tkleisas/groovebox/docs/themes.png

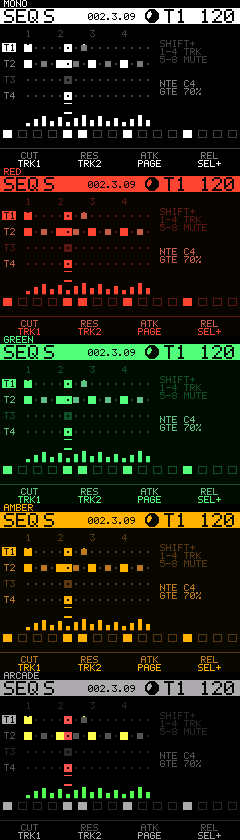
docs/themes.png
