tkleisas/groovebox/docs/widgets.png

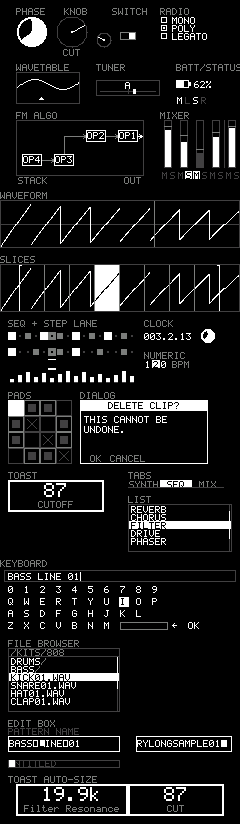
docs/widgets.png
