tkleisas/groovebox/nsr2/panel_mockup_nsr2.png

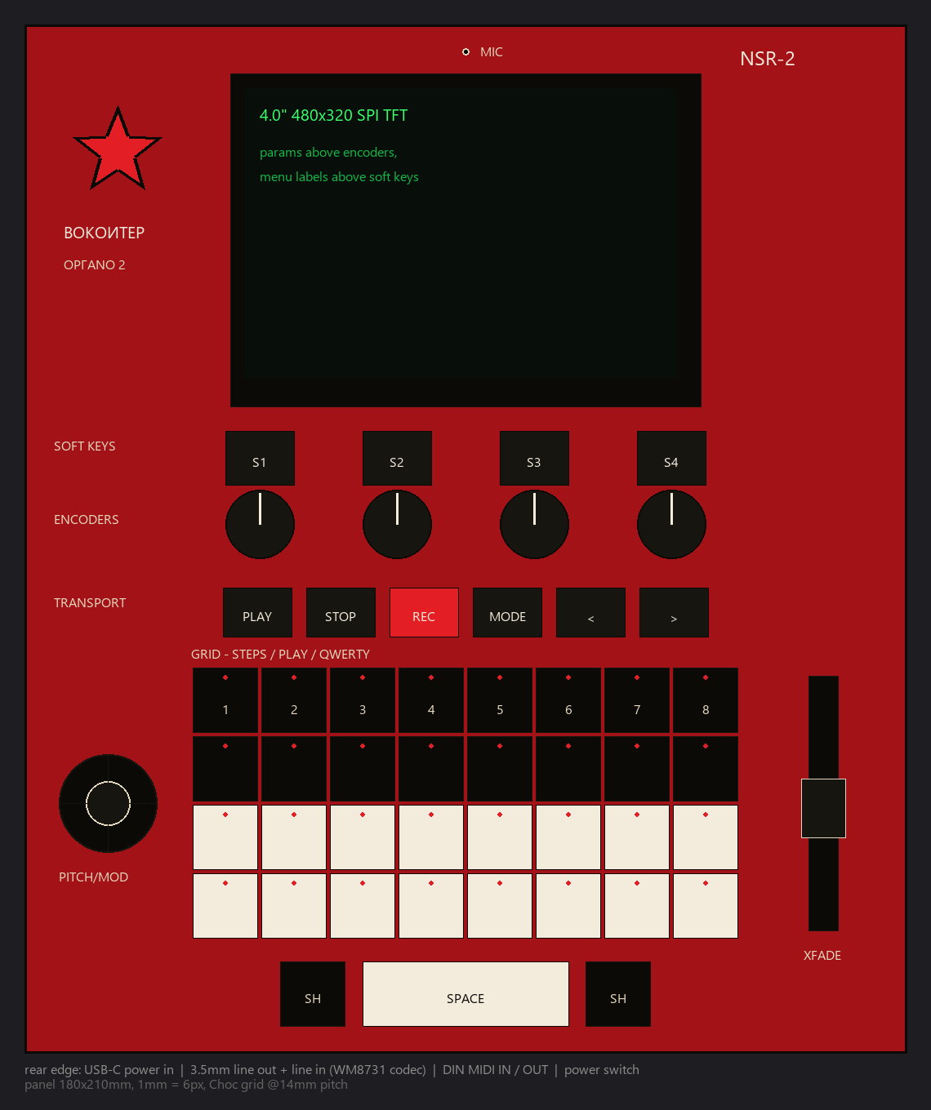
nsr2/panel_mockup_nsr2.png
