tkleisas/groovebox/nsr2/hardware/brain/brain.kicad_sch

## KiCad design nsr2/hardware/brain/brain.kicad_sch (2026-09-04)

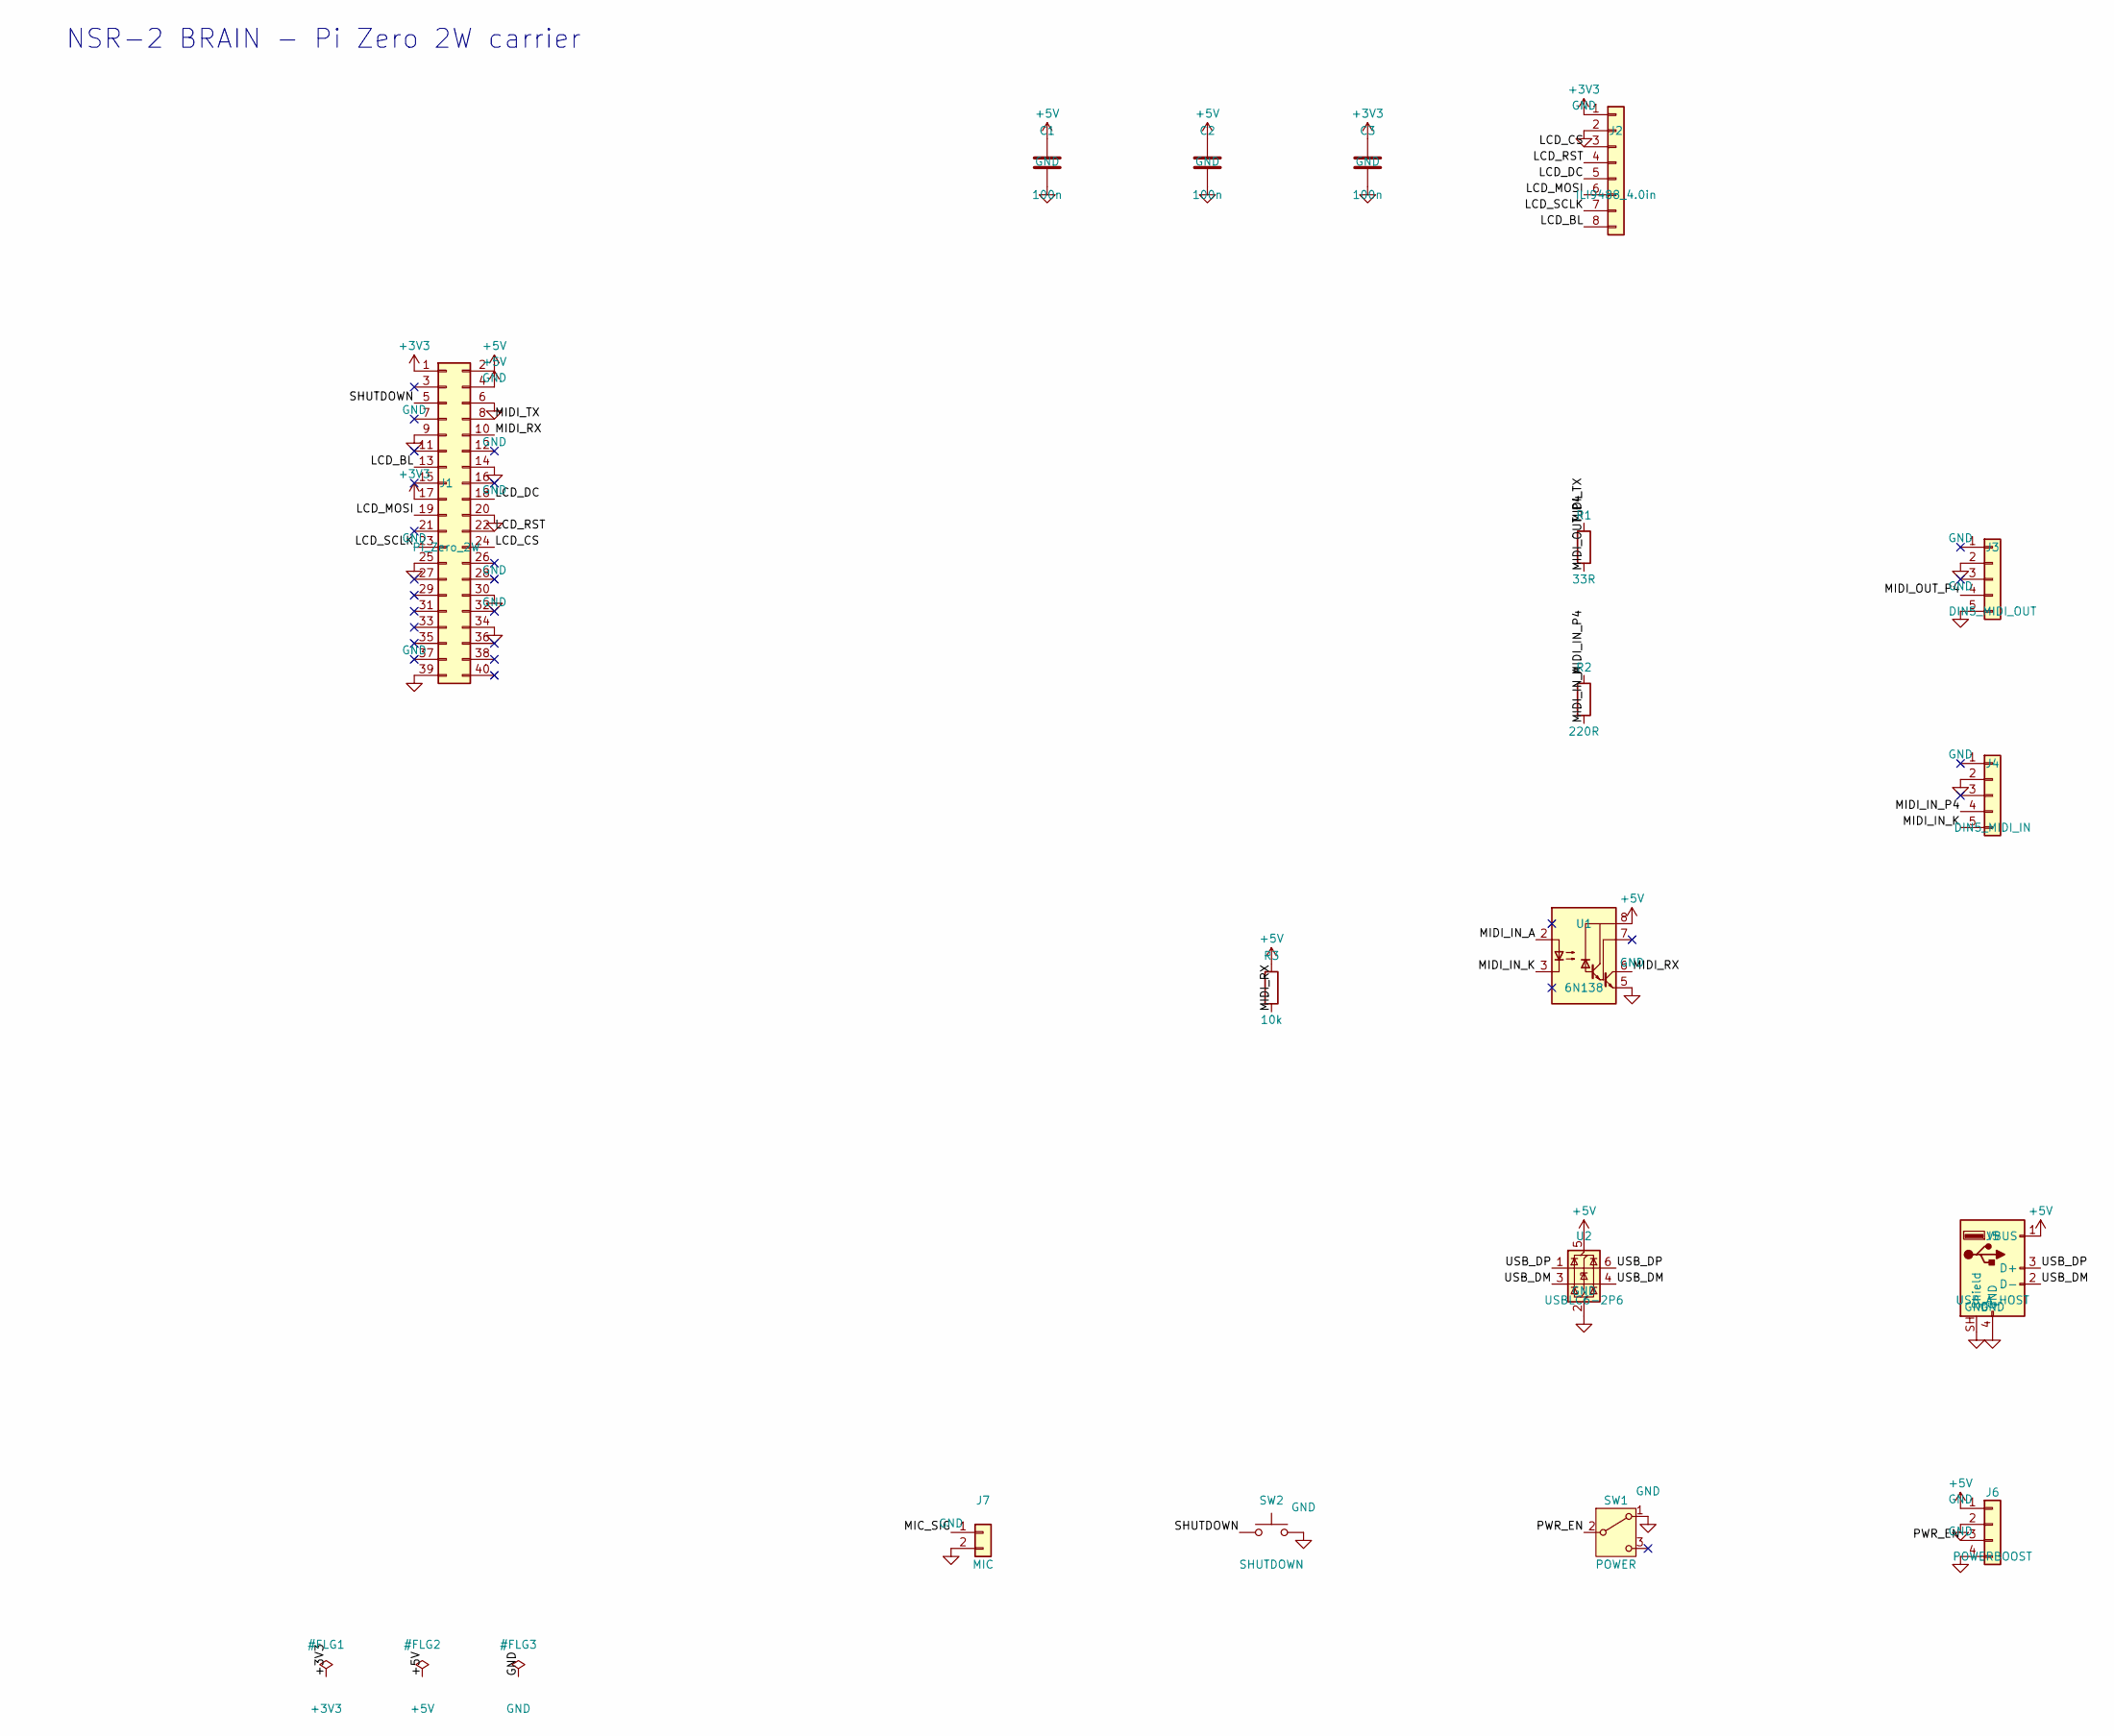
[picture p11: schematic brain.kicad_sch]

Parts:
C1, C2, C3: 100n; C_0805_2012Metric
J1: Pi_Zero_2W; PinSocket_2x20_P2.54mm_Vertical
J2: ILI9488_4.0in; PinHeader_1x08_P2.54mm_Horizontal
J3: DIN5_MIDI_OUT; DIN5-RA-PTH
J4: DIN5_MIDI_IN; DIN5-RA-PTH
J5: USB_A_HOST; USB_A_Connfly_DS1098_Horizontal
J6: POWERBOOST; JST_XH_B4B-XH-A_1x04_P2.50mm_Vertical
J7: MIC; JST_XH_B2B-XH-A_1x02_P2.50mm_Vertical
R1: 33R; R_0805_2012Metric
R2: 220R; R_0805_2012Metric
R3: 10k; R_0805_2012Metric
SW1: POWER; SW_SPDT_SLIDE_THT
SW2: SHUTDOWN; SW_PUSH_6mm
U1: 6N138; DIP-8_W7.62mm
U2: USBLC6-2P6; SOT-23-6

Connections:
+3V3: C3.1, J1.1, J1.17, J2.1
+5V: C1.1, C2.1, J1.2, J1.4, J5.1 (VBUS), J6.1, R3.1, U1.8 (VCC), U2.5 (VBUS)
GND: C1.2, C2.2, C3.2, J1.6, J1.9, J1.14, J1.20, J1.25, J1.30, J1.34, J1.39, J2.2, J3.2, J3.5, J4.2, J5.4 (GND), J5.SH (Shield), J6.2, J6.4, J7.2, SW1.1 (A), SW2.2, U1.5 (GND), U2.2 (GND)
LCD_BL: J1.13, J2.8
LCD_CS: J1.24, J2.3
LCD_DC: J1.18, J2.5
LCD_MOSI: J1.19, J2.6
LCD_RST: J1.22, J2.4
LCD_SCLK: J1.23, J2.7
MIC_SIG: J7.1
MIDI_IN_A: R2.2, U1.2 (C1)
MIDI_IN_K: J4.5, U1.3 (C2)
MIDI_IN_P4: J4.4, R2.1
MIDI_OUT_P4: J3.4, R1.2
MIDI_RX: J1.10, R3.2, U1.6 (VO2)
MIDI_TX: J1.8, R1.1
PWR_EN: J6.3, SW1.2 (B)
SHUTDOWN: J1.5, SW2.1
USB_DM: J5.2 (D-), U2.3 (I/O2), U2.4 (I/O2)
USB_DP: J5.3 (D+), U2.1 (I/O1), U2.6 (I/O1)

Notes on the sheet:
NSR-2 BRAIN - Pi Zero 2W carrier
