tkleisas/groovebox/nsr2/hardware/io/io.kicad_sch

## KiCad design nsr2/hardware/io/io.kicad_sch (2026-09-04)

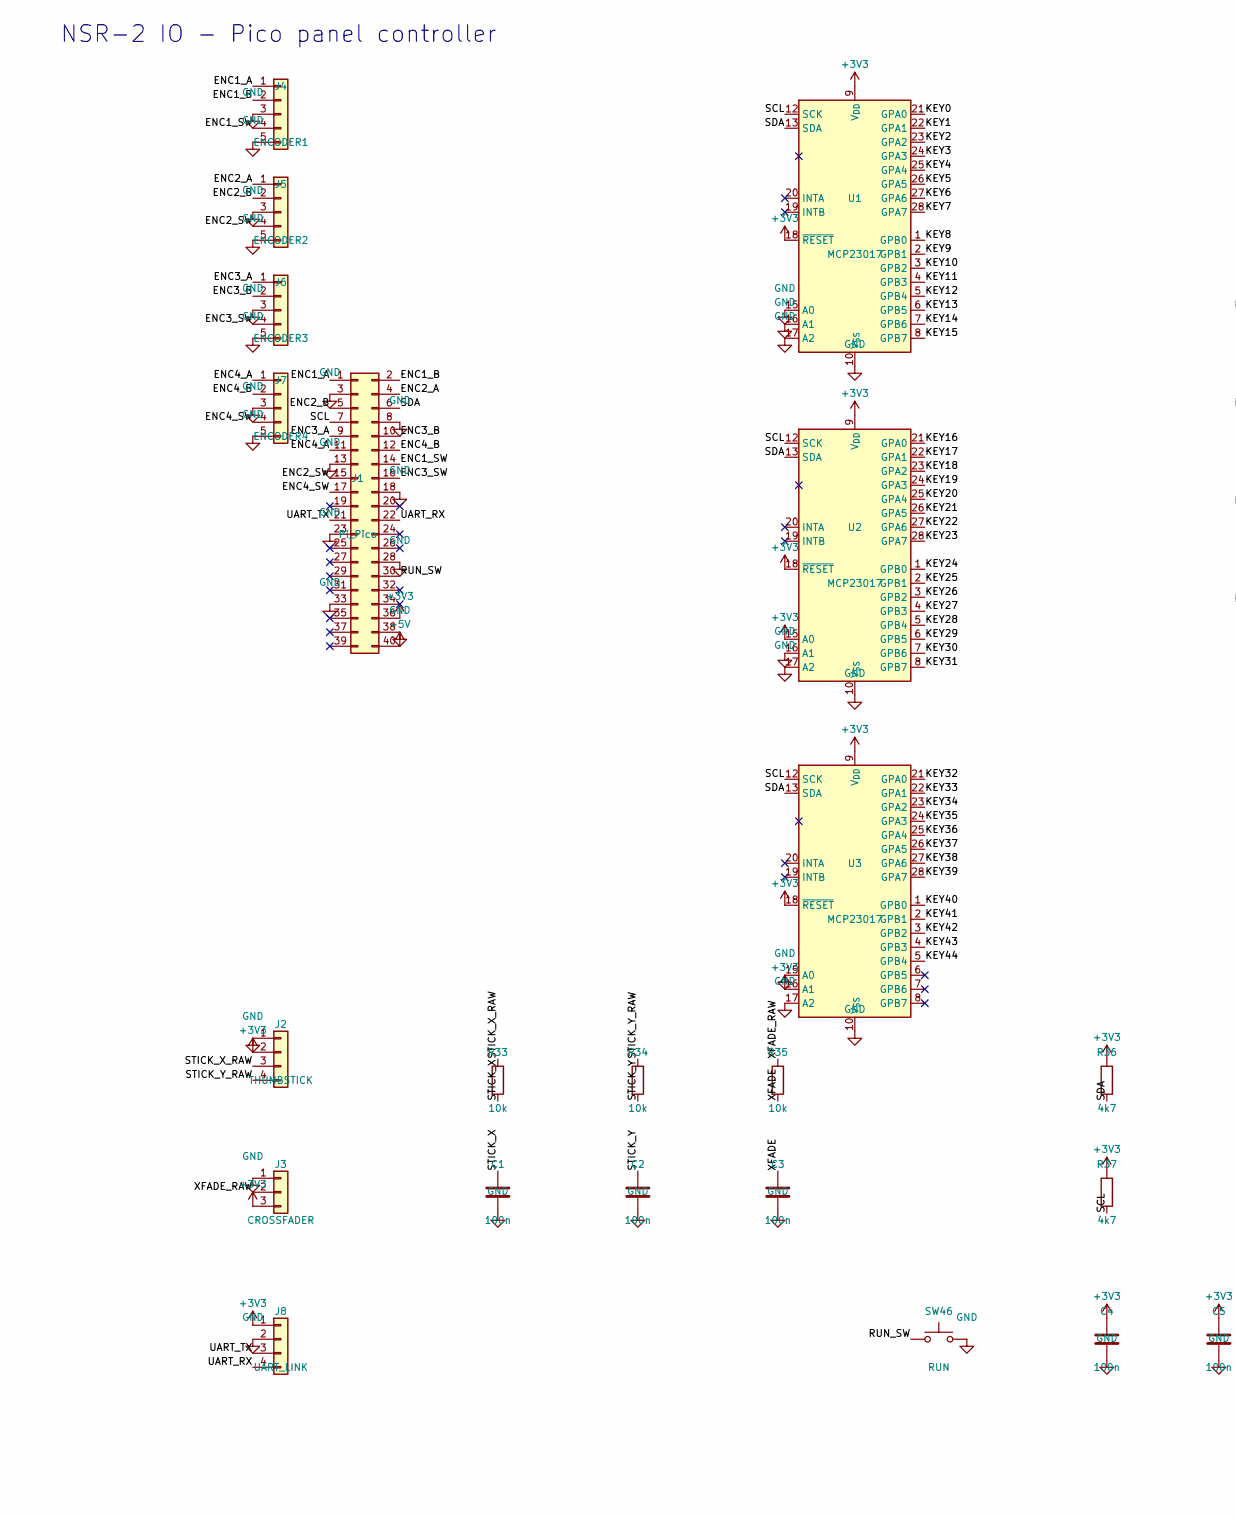
[picture p12: schematic io.kicad_sch, part in row 1, column 1]

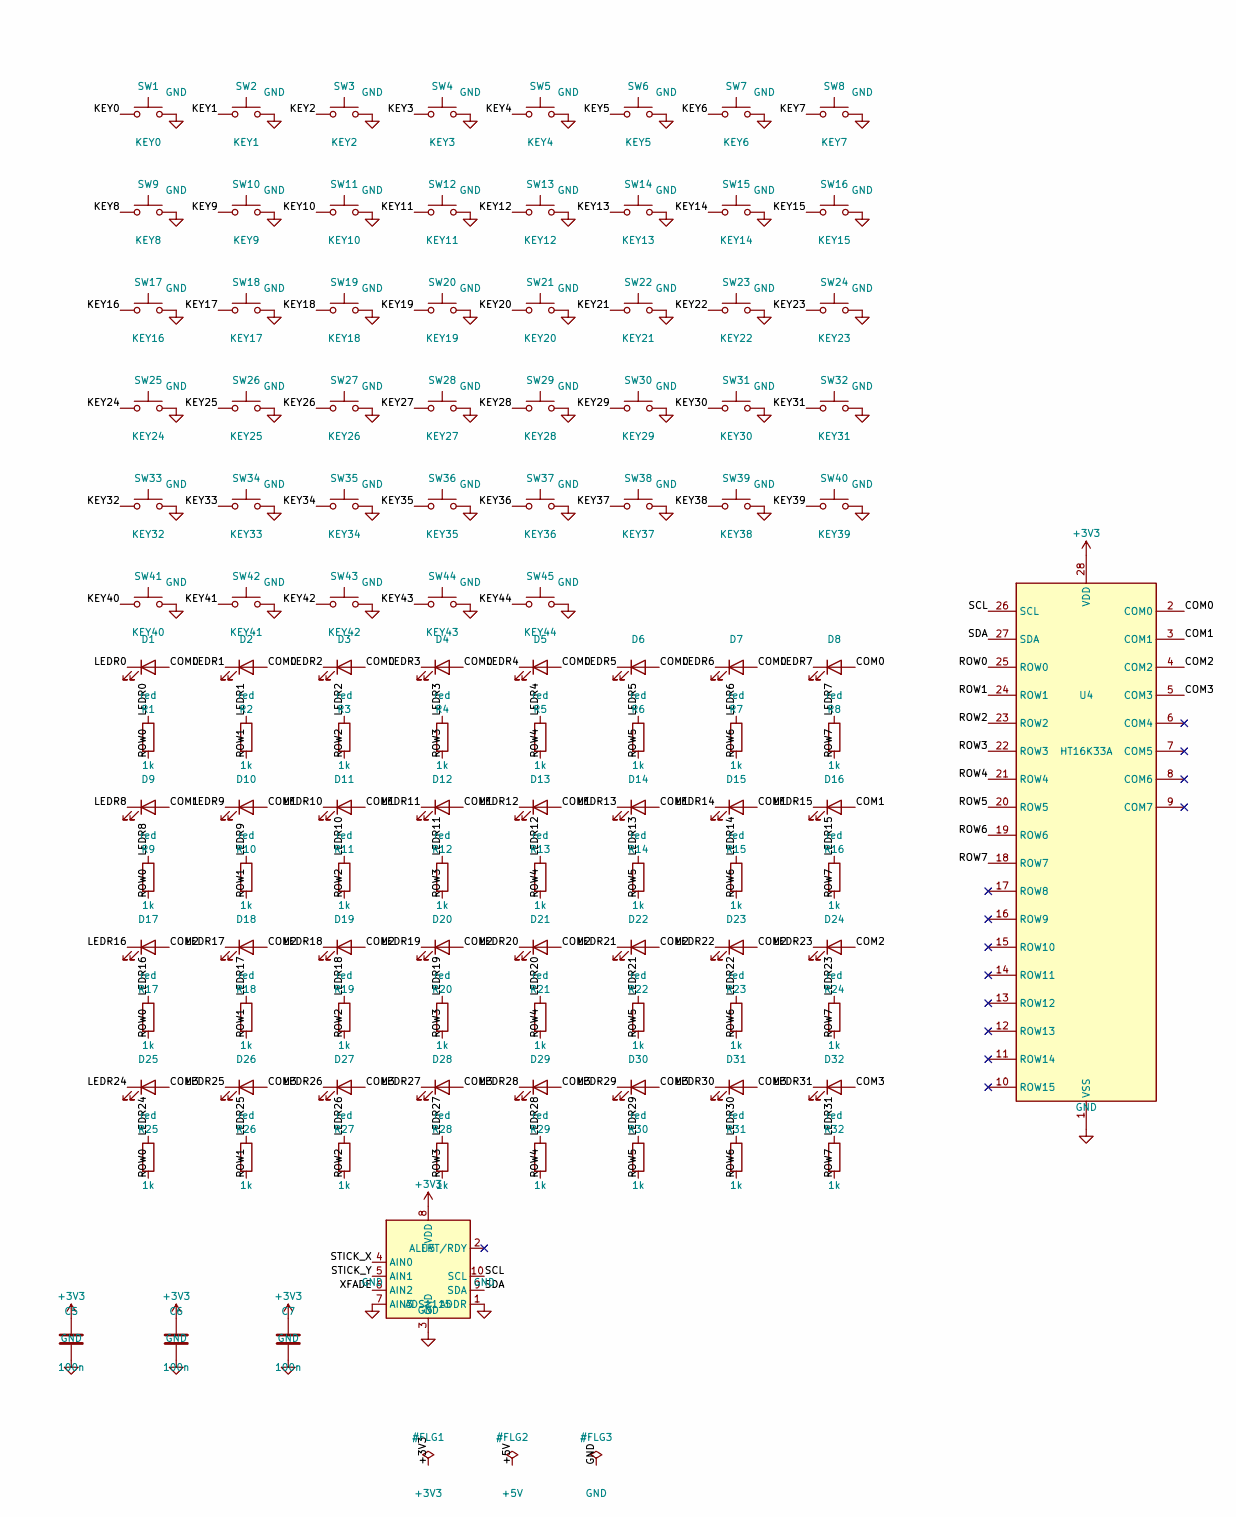
[picture p13: schematic io.kicad_sch, part in row 1, column 2]

Parts:
C1, C2, C3, C4, C5, C6, C7: 100n; C_0805_2012Metric
D1, D2, D3, D4, D5, D6, D7, D8, D9, D10, D11, D12, D13, D14, D15, D16, D17, D18, D19, D20, D21, D22, D23, D24, D25, D26, D27, D28, D29, D30, D31, D32: red; LED_0603_1608Metric
J1: Pi_Pico; PinSocket_2x20_P2.54mm_Vertical
J2: THUMBSTICK; JST_XH_B4B-XH-A_1x04_P2.50mm_Vertical
J3: CROSSFADER; JST_XH_B3B-XH-A_1x03_P2.50mm_Vertical
J4: ENCODER1; JST_XH_B5B-XH-A_1x05_P2.50mm_Vertical
J5: ENCODER2; JST_XH_B5B-XH-A_1x05_P2.50mm_Vertical
J6: ENCODER3; JST_XH_B5B-XH-A_1x05_P2.50mm_Vertical
J7: ENCODER4; JST_XH_B5B-XH-A_1x05_P2.50mm_Vertical
J8: UART_LINK; JST_XH_B4B-XH-A_1x04_P2.50mm_Vertical
R1, R2, R3, R4, R5, R6, R7, R8, R9, R10, R11, R12, R13, R14, R15, R16, R17, R18, R19, R20, R21, R22, R23, R24, R25, R26, R27, R28, R29, R30, R31, R32: 1k; R_0805_2012Metric
R33, R34, R35: 10k; R_0805_2012Metric
R36, R37: 4k7; R_0805_2012Metric
SW1: KEY0; SW_Hotswap_Kailh_Choc_V1
SW2: KEY1; SW_Hotswap_Kailh_Choc_V1
SW3: KEY2; SW_Hotswap_Kailh_Choc_V1
SW4: KEY3; SW_Hotswap_Kailh_Choc_V1
SW5: KEY4; SW_Hotswap_Kailh_Choc_V1
SW6: KEY5; SW_Hotswap_Kailh_Choc_V1
SW7: KEY6; SW_Hotswap_Kailh_Choc_V1
SW8: KEY7; SW_Hotswap_Kailh_Choc_V1
SW9: KEY8; SW_Hotswap_Kailh_Choc_V1
SW10: KEY9; SW_Hotswap_Kailh_Choc_V1
SW11: KEY10; SW_Hotswap_Kailh_Choc_V1
SW12: KEY11; SW_Hotswap_Kailh_Choc_V1
SW13: KEY12; SW_Hotswap_Kailh_Choc_V1
SW14: KEY13; SW_Hotswap_Kailh_Choc_V1
SW15: KEY14; SW_Hotswap_Kailh_Choc_V1
SW16: KEY15; SW_Hotswap_Kailh_Choc_V1
SW17: KEY16; SW_Hotswap_Kailh_Choc_V1
SW18: KEY17; SW_Hotswap_Kailh_Choc_V1
SW19: KEY18; SW_Hotswap_Kailh_Choc_V1
SW20: KEY19; SW_Hotswap_Kailh_Choc_V1
SW21: KEY20; SW_Hotswap_Kailh_Choc_V1
SW22: KEY21; SW_Hotswap_Kailh_Choc_V1
SW23: KEY22; SW_Hotswap_Kailh_Choc_V1
SW24: KEY23; SW_Hotswap_Kailh_Choc_V1
SW25: KEY24; SW_Hotswap_Kailh_Choc_V1
SW26: KEY25; SW_Hotswap_Kailh_Choc_V1
SW27: KEY26; SW_Hotswap_Kailh_Choc_V1
SW28: KEY27; SW_Hotswap_Kailh_Choc_V1
SW29: KEY28; SW_Hotswap_Kailh_Choc_V1
SW30: KEY29; SW_Hotswap_Kailh_Choc_V1
SW31: KEY30; SW_Hotswap_Kailh_Choc_V1
SW32: KEY31; SW_Hotswap_Kailh_Choc_V1
SW33: KEY32; SW_Hotswap_Kailh_Choc_V1
SW34: KEY33; SW_Hotswap_Kailh_Choc_V1
SW35: KEY34; SW_Hotswap_Kailh_Choc_V1
SW36: KEY35; SW_Hotswap_Kailh_Choc_V1
SW37: KEY36; SW_Hotswap_Kailh_Choc_V1
SW38: KEY37; SW_Hotswap_Kailh_Choc_V1
SW39: KEY38; SW_Hotswap_Kailh_Choc_V1
SW40: KEY39; SW_Hotswap_Kailh_Choc_V1
SW41: KEY40; SW_Hotswap_Kailh_Choc_V1
SW42: KEY41; SW_Hotswap_Kailh_Choc_V1
SW43: KEY42; SW_Hotswap_Kailh_Choc_V1
SW44: KEY43; SW_Hotswap_Kailh_Choc_V1
SW45: KEY44; SW_Hotswap_Kailh_Choc_V1
SW46: RUN; SW_PUSH_6mm
U1, U2, U3: MCP23017; SSOP-28_5.3x10.2mm_P0.65mm
U4: HT16K33A; SSOP-28_5.3x10.2mm_P0.65mm
U5: ADS1115; MSOP-10_3x3mm_P0.5mm

Connections:
+3V3: C4.1, C5.1, C6.1, C7.1, J1.36, J2.2, J3.3, J8.1, R36.1, R37.1, U1.9 (V_{DD}), U1.18 (~RESET), U2.9 (V_{DD}), U2.15 (A0), U2.18 (~RESET), U3.9 (V_{DD}), U3.16 (A1), U3.18 (~RESET), U4.28 (VDD), U5.8 (VDD)
+5V: J1.40
COM0: D1.2 (A), D2.2 (A), D3.2 (A), D4.2 (A), D5.2 (A), D6.2 (A), D7.2 (A), D8.2 (A), U4.2 (COM0)
COM1: D9.2 (A), D10.2 (A), D11.2 (A), D12.2 (A), D13.2 (A), D14.2 (A), D15.2 (A), D16.2 (A), U4.3 (COM1)
COM2: D17.2 (A), D18.2 (A), D19.2 (A), D20.2 (A), D21.2 (A), D22.2 (A), D23.2 (A), D24.2 (A), U4.4 (COM2)
COM3: D25.2 (A), D26.2 (A), D27.2 (A), D28.2 (A), D29.2 (A), D30.2 (A), D31.2 (A), D32.2 (A), U4.5 (COM3)
ENC1_A: J1.1, J4.1
ENC1_B: J1.2, J4.2
ENC1_SW: J1.14, J4.4
ENC2_A: J1.4, J5.1
ENC2_B: J1.5, J5.2
ENC2_SW: J1.15, J5.4
ENC3_A: J1.9, J6.1
ENC3_B: J1.10, J6.2
ENC3_SW: J1.16, J6.4
ENC4_A: J1.11, J7.1
ENC4_B: J1.12, J7.2
ENC4_SW: J1.17, J7.4
GND: C1.2, C2.2, C3.2, C4.2, C5.2, C6.2, C7.2, J1.3, J1.8, J1.13, J1.18, J1.23, J1.28, J1.33, J1.38, J2.1, J3.1, J4.3, J4.5, J5.3, J5.5, J6.3, J6.5, J7.3, J7.5, J8.2, SW1.2, SW2.2, SW3.2, SW4.2, SW5.2, SW6.2, SW7.2, SW8.2, SW9.2, SW10.2, SW11.2, SW12.2, SW13.2, SW14.2, SW15.2, SW16.2, SW17.2, SW18.2, SW19.2, SW20.2, SW21.2, SW22.2, SW23.2, SW24.2, SW25.2, SW26.2, SW27.2, SW28.2, SW29.2, SW30.2, SW31.2, SW32.2, SW33.2, SW34.2, SW35.2, SW36.2, SW37.2, SW38.2, SW39.2, SW40.2, SW41.2, SW42.2, SW43.2, SW44.2, SW45.2, SW46.2, U1.10 (V_{SS}), U1.15 (A0), U1.16 (A1), U1.17 (A2), U2.10 (V_{SS}), U2.16 (A1), U2.17 (A2), U3.10 (V_{SS}), U3.15 (A0), U3.17 (A2), U4.1 (VSS), U5.1 (ADDR), U5.3 (GND), U5.7 (AIN3)
KEY0: SW1.1, U1.21 (GPA0)
KEY1: SW2.1, U1.22 (GPA1)
KEY2: SW3.1, U1.23 (GPA2)
KEY3: SW4.1, U1.24 (GPA3)
KEY4: SW5.1, U1.25 (GPA4)
KEY5: SW6.1, U1.26 (GPA5)
KEY6: SW7.1, U1.27 (GPA6)
KEY7: SW8.1, U1.28 (GPA7)
KEY8: SW9.1, U1.1 (GPB0)
KEY9: SW10.1, U1.2 (GPB1)
KEY10: SW11.1, U1.3 (GPB2)
KEY11: SW12.1, U1.4 (GPB3)
KEY12: SW13.1, U1.5 (GPB4)
KEY13: SW14.1, U1.6 (GPB5)
KEY14: SW15.1, U1.7 (GPB6)
KEY15: SW16.1, U1.8 (GPB7)
KEY16: SW17.1, U2.21 (GPA0)
KEY17: SW18.1, U2.22 (GPA1)
KEY18: SW19.1, U2.23 (GPA2)
KEY19: SW20.1, U2.24 (GPA3)
KEY20: SW21.1, U2.25 (GPA4)
KEY21: SW22.1, U2.26 (GPA5)
KEY22: SW23.1, U2.27 (GPA6)
KEY23: SW24.1, U2.28 (GPA7)
KEY24: SW25.1, U2.1 (GPB0)
KEY25: SW26.1, U2.2 (GPB1)
KEY26: SW27.1, U2.3 (GPB2)
KEY27: SW28.1, U2.4 (GPB3)
KEY28: SW29.1, U2.5 (GPB4)
KEY29: SW30.1, U2.6 (GPB5)
KEY30: SW31.1, U2.7 (GPB6)
KEY31: SW32.1, U2.8 (GPB7)
KEY32: SW33.1, U3.21 (GPA0)
KEY33: SW34.1, U3.22 (GPA1)
KEY34: SW35.1, U3.23 (GPA2)
KEY35: SW36.1, U3.24 (GPA3)
KEY36: SW37.1, U3.25 (GPA4)
KEY37: SW38.1, U3.26 (GPA5)
KEY38: SW39.1, U3.27 (GPA6)
KEY39: SW40.1, U3.28 (GPA7)
KEY40: SW41.1, U3.1 (GPB0)
KEY41: SW42.1, U3.2 (GPB1)
KEY42: SW43.1, U3.3 (GPB2)
KEY43: SW44.1, U3.4 (GPB3)
KEY44: SW45.1, U3.5 (GPB4)
LEDR0: D1.1 (K), R1.1
LEDR1: D2.1 (K), R2.1
LEDR2: D3.1 (K), R3.1
LEDR3: D4.1 (K), R4.1
LEDR4: D5.1 (K), R5.1
LEDR5: D6.1 (K), R6.1
LEDR6: D7.1 (K), R7.1
LEDR7: D8.1 (K), R8.1
LEDR8: D9.1 (K), R9.1
LEDR9: D10.1 (K), R10.1
LEDR10: D11.1 (K), R11.1
LEDR11: D12.1 (K), R12.1
LEDR12: D13.1 (K), R13.1
LEDR13: D14.1 (K), R14.1
LEDR14: D15.1 (K), R15.1
LEDR15: D16.1 (K), R16.1
LEDR16: D17.1 (K), R17.1
LEDR17: D18.1 (K), R18.1
LEDR18: D19.1 (K), R19.1
LEDR19: D20.1 (K), R20.1
LEDR20: D21.1 (K), R21.1
LEDR21: D22.1 (K), R22.1
LEDR22: D23.1 (K), R23.1
LEDR23: D24.1 (K), R24.1
LEDR24: D25.1 (K), R25.1
LEDR25: D26.1 (K), R26.1
LEDR26: D27.1 (K), R27.1
LEDR27: D28.1 (K), R28.1
LEDR28: D29.1 (K), R29.1
LEDR29: D30.1 (K), R30.1
LEDR30: D31.1 (K), R31.1
LEDR31: D32.1 (K), R32.1
ROW0: R1.2, R9.2, R17.2, R25.2, U4.25 (ROW0)
ROW1: R2.2, R10.2, R18.2, R26.2, U4.24 (ROW1)
ROW2: R3.2, R11.2, R19.2, R27.2, U4.23 (ROW2)
ROW3: R4.2, R12.2, R20.2, R28.2, U4.22 (ROW3)
ROW4: R5.2, R13.2, R21.2, R29.2, U4.21 (ROW4)
ROW5: R6.2, R14.2, R22.2, R30.2, U4.20 (ROW5)
ROW6: R7.2, R15.2, R23.2, R31.2, U4.19 (ROW6)
ROW7: R8.2, R16.2, R24.2, R32.2, U4.18 (ROW7)
RUN_SW: J1.30, SW46.1
SCL: J1.7, R37.2, U1.12 (SCK), U2.12 (SCK), U3.12 (SCK), U4.26 (SCL), U5.10 (SCL)
SDA: J1.6, R36.2, U1.13 (SDA), U2.13 (SDA), U3.13 (SDA), U4.27 (SDA), U5.9 (SDA)
STICK_X: C1.1, R33.2, U5.4 (AIN0)
STICK_X_RAW: J2.3, R33.1
STICK_Y: C2.1, R34.2, U5.5 (AIN1)
STICK_Y_RAW: J2.4, R34.1
UART_RX: J1.22, J8.4
UART_TX: J1.21, J8.3
XFADE: C3.1, R35.2, U5.6 (AIN2)
XFADE_RAW: J3.2, R35.1

Notes on the sheet:
NSR-2 IO - Pico panel controller
