tkleisas/groovebox/emulator/src/ui.h

#pragma once

// Tiny software renderer for the 240x160 RGB565 display, in the style
// of docs/ui_mockup.png (Elektron-like, monochrome): inverted header
// bar (page name + BPM), parameter rows (dim name, bright value, bar),
// inverse-video selected row, LED row, footer with encoder / soft-key
// assignments.
//
// Pages (UiState::page): 0 = SYNTH (param rows), 1 = SEQ
// (SequencerWidget), 2 = MIXER (MixerWidget). Widget geometry lives in
// widgets.h; all widget bboxes follow the 8 px grid rule.

#include <cstdint>
#include "font5x7.h"
#include "hal.h" // kDisplayW / kDisplayH
#include "widgets.h"

namespace gb {

struct UiParam {
    const char* name;
    int value; // 0..127; -1 = unbound (renders dim "—")
};

struct UiState {
    const char* pageName = "SYNTH"; // page 0 title (SYNTH / DRUMS)
    // INST page on drum tracks: the edit pad (last-played voice), drawn
    // inverse-video in the header. nullptr on melodic tracks.
    const char* padName = nullptr;
    int page = 0;           // 0 = SYNTH, 1 = SEQ, 2 = MIXER
    int track = 0;          // 0-based engine track shown in header
    double bpm = 120.0;
    bool playing = false;
    bool recording = false;
    int mode = 0;           // 0 = PLAY, 1 = SEQ
    int selected = 0;       // selected parameter row (inverse video)
    UiParam params[6] = {
        {"CUTOFF",  87},
        {"RESO",    41},
        {"ATTACK",   3},
        {"DECAY",   55},
        {"SUSTAIN", 70},
        {"RELEASE", 24},
    };
    const char* encLabels[4]  = {"CUT", "RES", "ATK", "REL"};
    const char* softLabels[4] = {"TRK1", "TRK2", "PAGE", "SEL+"};
    // Optional one-liner drawn between the LED row and the footer
    // (UTF-8 — used by the smoke test to demo Greek/Cyrillic).
    const char* overlayLine = nullptr;
    bool leds[16] = {};

    // Transport clock (drawn in the SEQ page header, live data).
    int clockBar = 1, clockBeat = 1, clockStep = 1;
    float clockPhase = 0.0f;

    // SEQ page: T1 default note / gate readout (right info block).
    int seqNote = 60;
    int seqGatePct = 70;
    // SEQ page: pattern length + 16-step window (paging) state.
    int seqLength = 16;
    int seqWindow = 0;      // first step of the visible window
    bool lenEdit = false;   // length-edit state active (S1 = LEN)

    // Toast overlay (transient encoder feedback; app-owned text).
    bool toastActive = false;
    char toastLabel[16] = {};
    char toastValue[16] = {};

    // Page 1 / 2 widget state (app-owned, updated each frame).
    SequencerWidget seq;
    StepLaneWidget lane;   // per-step velocity of the selected track
    MixerWidget mixer;

    // FX page (page 3): two insert slots on the selected track.
    const char* fxName = nullptr;  // nullptr = EMPTY (current slot)
    bool fxBypassed = false;
    int fxSlot = 0;                // insert slot 0/1 (shown as 1/2)
    UiParam fxParams[4] = {};      // first 4 effect params (-1 unbound)

    // MFX page (page 7): one MIDI-effect slot per track.
    const char* mfxName = nullptr;
    bool mfxBypassed = false;
    UiParam mfxParams[4] = {};

    // TRACK page (page 8)
    int trackType = 1;             // 0=AUDIO 1=MIDI
    float trackVol = 1.0f, trackPan = 0.0f;
    int trackInputCh = 0;
    bool trackMonitor = false;
    bool trackHasClip = false;
    // effect chooser (ListWidget overlay on the FX page)
    bool chooserOpen = false;
    const char* const* chooserItems = nullptr;
    int chooserCount = 0;
    int chooserSel = 0;
    int chooserScroll = 0;

    // SAMPLE page (page 4)
    int sampleState = 0;      // 0 idle, 1 recording, 2 review
    float sampleLevel = 0;    // input peak 0..1
    float sampleElapsed = 0;  // seconds recorded
    const float* sampleWave = nullptr;
    int sampleWaveLen = 0;
    float sampleTrim0 = 0.0f, sampleTrim1 = 1.0f;
    float sampleGain = 1.0f;
    const char* sampleMsg = nullptr; // e.g. "NO INPUT"

    // LOAD page (page 5): file browser state
    FileBrowserWidget browser;

    // SETTINGS page (page 6)
    int settingsSel = 0;               // 0..3
    const char* settingsVal[4] = {};   // value strings per row

    // Macro encoder (5-8) bindings, shown as a strip on the SYNTH page
    const char* macroLabels[4] = {};

    // NSR-2 additions
    bool nsr2 = false;
    const char* textBuf = nullptr;     // text-entry mode buffer
    int textCursor = 0;
    int scaleLock = 2;                 // 0=major 1=minor 2=chromatic

    // confirm dialog overlay
    bool dialogActive = false;
    const char* dlgTitle = nullptr;
    const char* dlgLine = nullptr;
};

class Ui {
public:
    // fb must point to 240x160 uint16 RGB565 pixels.
    void render(const UiState& s, uint16_t* fb);

    // Boot splash ("ПОЕХАЛИ!" + brand line), themed. Drawn instead of
    // any page for the first moments after startup.
    void renderSplash(uint16_t* fb);

private:
    Font5x7 m_font;

    void drawHeader(const UiState& s, uint16_t* fb);
    void drawLeds(const UiState& s, uint16_t* fb);
    void drawFooter(const UiState& s, uint16_t* fb);
    void drawParamRow(const UiParam& p, int y0, bool sel, uint16_t* fb);
    void pageSynth(const UiState& s, uint16_t* fb);
    void pageSeq(const UiState& s, uint16_t* fb);
    void pageMixer(const UiState& s, uint16_t* fb);
    void pageFx(const UiState& s, uint16_t* fb);
    void pageMfx(const UiState& s, uint16_t* fb);
    void pageTrack(const UiState& s, uint16_t* fb);
    void pageSample(const UiState& s, uint16_t* fb);
    void pageLoad(const UiState& s, uint16_t* fb);
    void pageSettings(const UiState& s, uint16_t* fb);

    static void fill(uint16_t* fb, int x, int y, int w, int h, uint16_t c);
    static void frame(uint16_t* fb, int x, int y, int w, int h, uint16_t c);
    // Returns advance in pixels. When bg is opaque (inv=true), every
    // glyph cell is painted fg-on-bg (used for inverse-video rows).
    // s is UTF-8; width is measured in codepoints, not bytes.
    int text(uint16_t* fb, int x, int y, int scale, const char* s,
             uint16_t fg, bool inv = false, uint16_t bg = 0);
    // Pixel width of a UTF-8 string at the given scale (codepoints).
    static int textWidth(const char* s, int scale) {
        return utf8Length(s) * (Font5x7::kW + 1) * scale;
    }
};

} // namespace gb
